rus1ru/SmartSense-EN1190/firmware/dataset/threshold_score_is_high_accel_3.png

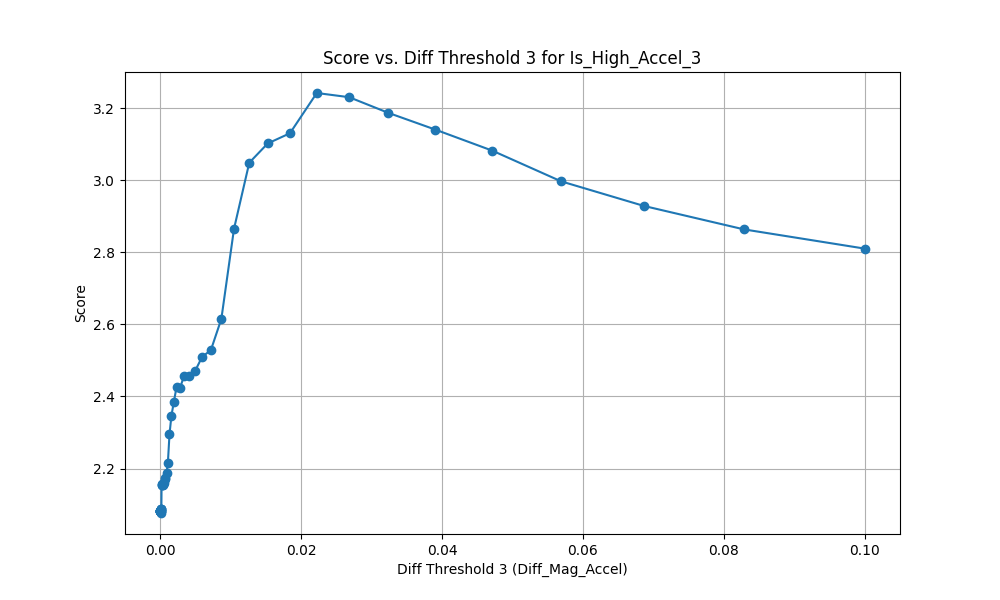
firmware/dataset/threshold_score_is_high_accel_3.png
