rus1ru/SmartSense-EN1190/cad_files/Assemblies/Assembly_Knob.SLDASM

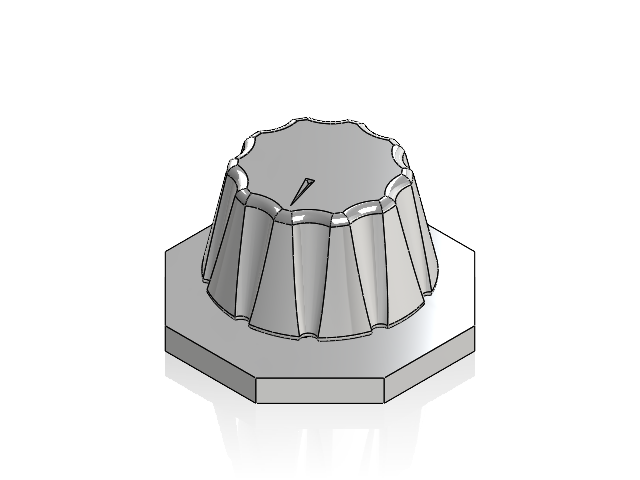
[picture p41: CAD file, 2026-03-15]
cad_files/Assemblies/Assembly_Knob.SLDASM
Encoder1
Encoder2
