rus1ru/SmartSense-EN1190/firmware/ss_motion_unit/include/ulp_main.h

/*
    Put your ULP globals here you want visibility
    for your sketch. Add "ulp_" to the beginning
    of the variable name and must be size 'uint32_t'
*/
#include "Arduino.h"

extern uint32_t ulp_entry;
extern uint32_t ulp_count;
