rus1ru/SmartSense-EN1190/firmware/test_codes/MPU6050_test/MPU6050_test.ino

#include <Wire.h>
#include <MPU6050.h>

MPU6050 mpu;

void setup() {
  Serial.begin(115200);
  Wire.begin();
  mpu.initialize();

  if (mpu.testConnection()) {
    Serial.println("MPU6050 connection successful.");
  } else {
    Serial.println("MPU6050 connection failed.");
  }
}

void loop() {
  int16_t ax, ay, az;
  int16_t gx, gy, gz;

  mpu.getMotion6(&ax, &ay, &az, &gx, &gy, &gz);

  // Serial.print("a/g:\t");
  // Serial.print(ax); Serial.print("\t");
  // Serial.print(ay); Serial.print("\t");
  // Serial.print(az); Serial.print("\t");
  // Serial.print(gx); Serial.print("\t");
  // Serial.print(gy); Serial.print("\t");
  // Serial.print(gz); Serial.print("\t");

  int acclr_raw = (abs(ax)+abs(ay))/2;
  Serial.println((acclr_raw));
  String acclr = ((abs(ax)+abs(ay))/2 > 200) ? "yes":"no";
  // Serial.println(acclr);

  delay(50);
}
